ESilguero1/COTS/VSCode_Arduino_Project/src/Applications/LED_App.h

/***********************************************************************************************//**
 * @file       LED_App.h
  * @details    IMU application module. Services IMU initialization, data collection, and filtering
 * @author		Miguel Silguero
 * @copyright  Copyright (c) 2024-2025, Horizonless Embedded Solutions LLC
 * @date       03.09.2025 (created)
 *
 **************************************************************************************************/
#ifndef LED_App_H
#define LED_App_H

/***************************************************************************************************
 * INCLUDES
 **************************************************************************************************/
#include "Arduino.h"

/***************************************************************************************************
 * CONSTANTS AND DEFINITIONS
 **************************************************************************************************/
#define LED_FREQ_RATE_MS  (250)

/***************************************************************************************************
 * TYPEDEFS
 **************************************************************************************************/

/***************************************************************************************************
 * PUBLIC FUNCTION PROTOTYPES
 **************************************************************************************************/

class LED_App 
{
	public:
      	void Init(void);
		void Service_LED(void);
		void Set_LED_Code(uint8_t led_code);
		void Toggle_LED(void);
};
#endif
