ESilguero1/COTS/VSCode_Arduino_Project/src/Applications/BLE_Bridge_App.h

/***********************************************************************************************//**
 * @file       BLE_Bridge_App.h
 * @details
 * @author		Miguel Silguero
 * @copyright  Copyright (c) 2024-2025, Horizonless Embedded Solutions LLC
 * @date       07.01.2024 (created)
 *
 **************************************************************************************************/
#ifndef BLE_Bridge_App_H
#define BLE_Bridge_App_H

/***************************************************************************************************
 * INCLUDES
 **************************************************************************************************/
#include <SPI.h>
#include "Arduino.h"

/***************************************************************************************************
 * CONSTANTS AND DEFINITIONS
 **************************************************************************************************/

/***************************************************************************************************
 * TYPEDEFS
 **************************************************************************************************/

/***************************************************************************************************
 * PUBLIC FUNCTION PROTOTYPES
 **************************************************************************************************/
class BLE_Bridge_App 
{

	public:
      	uint8_t Init();
		void Service_BLE_UART();
		void println(const String &s);
};

#endif
