ESilguero1/COTS/VSCode_Arduino_Project/src/Applications/HWT906_App.h

/***********************************************************************************************//**
 * @file       HWT906_App.h
 * @details
 * @author		Miguel Silguero
 * @copyright  Copyright (c) 2024-2025, Horizonless Embedded Solutions LLC
 * @date       09.21.2025 (created)
 *
 **************************************************************************************************/
#ifndef BNO080_App_H
#define BNO080_App_H

/***************************************************************************************************
 * INCLUDES
 **************************************************************************************************/
#include "System_definitions.h"
#include <SPI.h>
#include "Arduino.h"

/***************************************************************************************************
 * CONSTANTS AND DEFINITIONS
 **************************************************************************************************/
#define IMU_DATA_ACQUSITION_PERIOD	(233)  //

/***************************************************************************************************
 * TYPEDEFS
 **************************************************************************************************/

/***************************************************************************************************
 * PUBLIC FUNCTION PROTOTYPES
 **************************************************************************************************/

class HWT906_App 
{
	public:
    	uint8_t Init(void);
		void CheckIMUDataCollection(void);
};
#endif
